deepanaishtaweera/HearingAid_Sem4/HearingAid/3D Files/9v-battery-3/preview.JPG

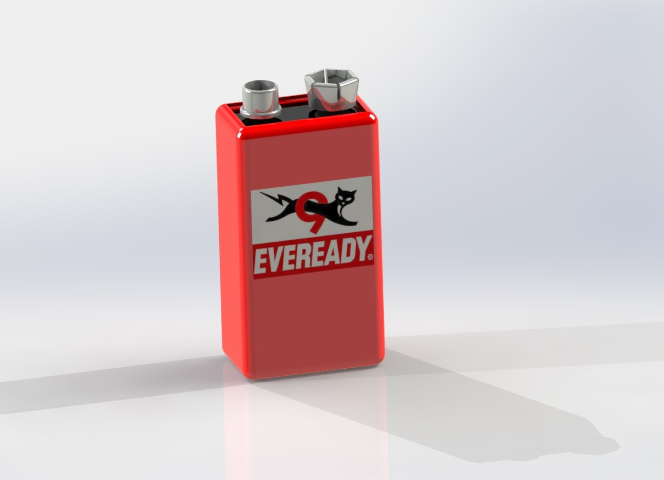
HearingAid/3D Files/9v-battery-3/preview.JPG
