deepanaishtaweera/HearingAid_Sem4/HearingAid/3D Files/female-audio-jack-3-5mm-3-pin-pth-1/Renderings/AB2_TRS_3p5MM_PTH_REF.jpg

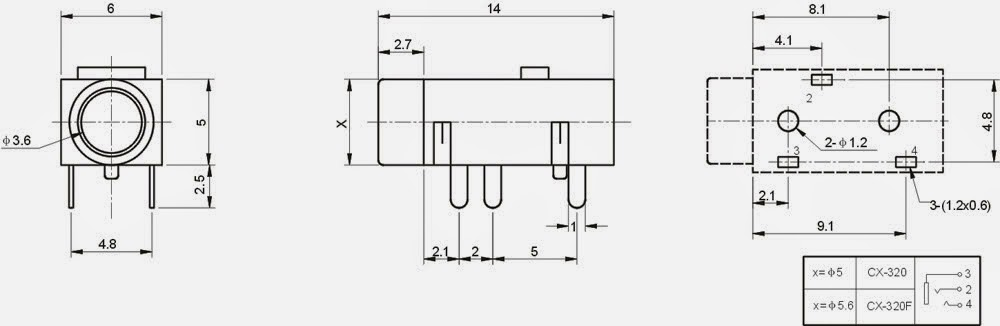
HearingAid/3D Files/female-audio-jack-3-5mm-3-pin-pth-1/Renderings/AB2_TRS_3p5MM_PTH_REF.jpg
