deepanaishtaweera/HearingAid_Sem4/HearingAid/3D Files/LM7805/ISO_view.JPG

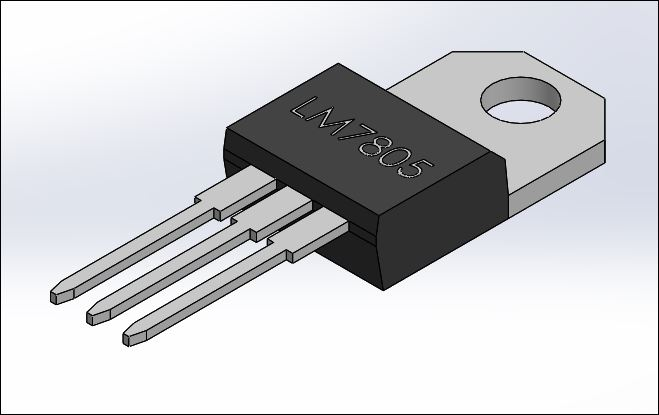
HearingAid/3D Files/LM7805/ISO_view.JPG
