deepanaishtaweera/HearingAid_Sem4/LTspiceCircuits/Pre-amplifier.asc

C1: cap; 33µ
C2: cap; 22µ
C3: cap; 33µ
Q1: npn; 2N2222
R1: res; 1.4k
R2: res; 10k
R3: res; 9k
R4: res; 18k
R5: res; 2k
V1: voltage; 3
V2: voltage; SINE(0 0.05 1k)
Named nets: 0
.tran 0.005s
